Ribbit-Network/ribbit-network-solar/hardware/solar-charger.kicad_sch

## KiCad design hardware/solar-charger.kicad_sch (2022-02-11, an earlier design)

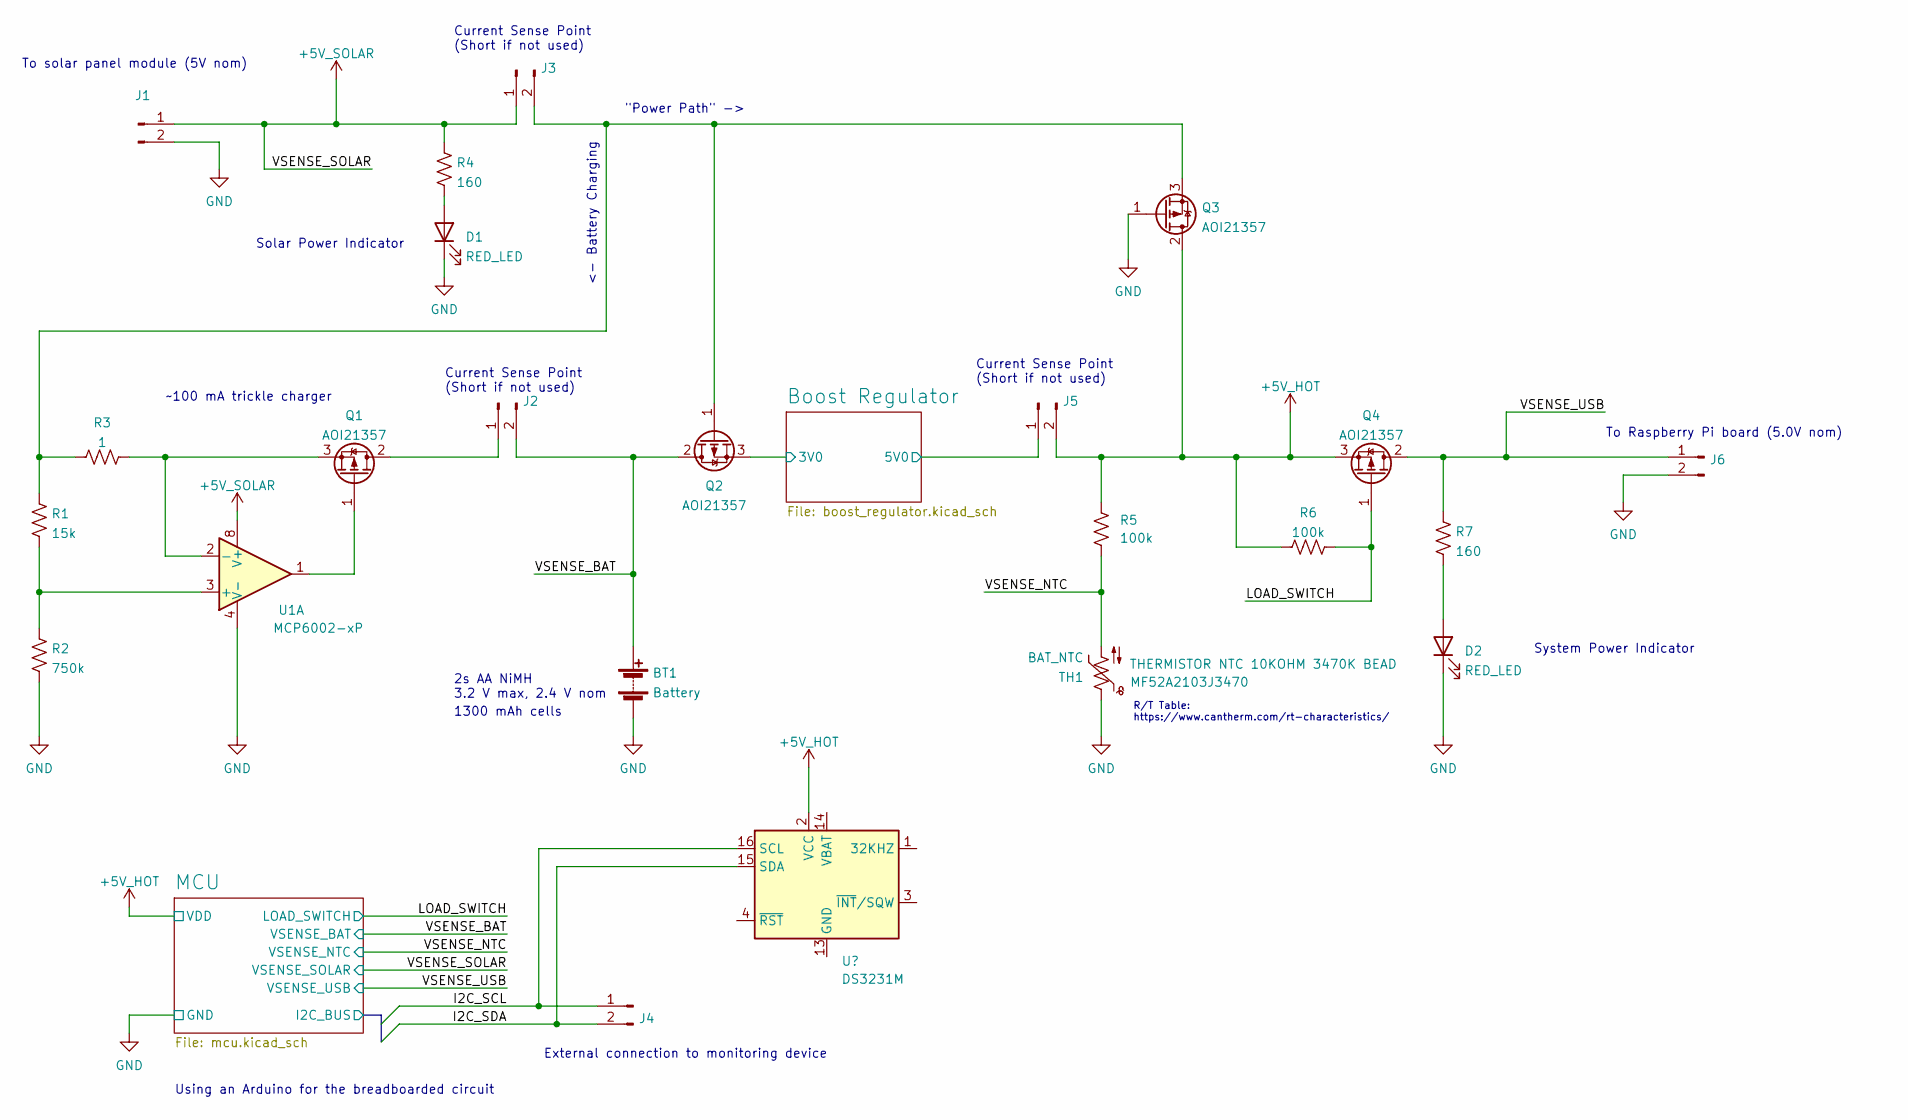
[picture p2: schematic solar-charger.kicad_sch]

Parts:
BT1: Battery
D1, D2: RED_LED
J1, J6: Conn_01x02_Male
J2, J3, J4: ISENSE_SOLAR
J5: ISENSE_DISCHARGE
Q1, Q2, Q3, Q4: AOI21357
R1: 15k
R2: 750k
R3: 1
R4, R7: 160
R5, R6: 100k
TH1: BAT_NTC; MPN MF52A2103J3470
U1: MCP6002-xP

Connections:
3V0: Q2.3 (S)
5V0: J5.1
+5V_HOT: J5.2, Q3.2 (D), Q4.3 (S), R5.1, R6.1
GND: BT1.2 (-), D1.1 (K), D2.1 (K), J1.2, J6.2, Q3.1 (G), R2.2, TH1.1, U1.4 (V-)
I2C_SCL: J4.1
I2C_SDA: J4.2
LOAD_SWITCH: Q4.1 (G), R6.2
unnamed: D1.2 (A), R4.2
unnamed: D2.2 (A), R7.2
unnamed: J2.1, Q1.2 (D)
unnamed: J3.2, Q2.1 (G), Q3.3 (S), R1.1, R3.1
unnamed: Q1.1 (G), U1.1
unnamed: Q1.3 (S), R3.2, U1.2 (-)
unnamed: R1.2, R2.1, U1.3 (+)
VSENSE_BAT: BT1.1 (+), J2.2, Q2.2 (D)
VSENSE_NTC: R5.2, TH1.2
VSENSE_SOLAR: J1.1, J3.1, R4.1
VSENSE_USB: J6.1, Q4.2 (D), R7.1

Notes on the sheet:
<- Battery Charging
To solar panel module (5V nom)
Solar Power Indicator
Current Sense Point (Short if not used)
~100 mA trickle charger
R/T Table: https://www.cantherm.com/rt-characteristics/
2s AA NiMH 3.2 V max, 2.4 V nom
"Power Path" ->
External connection to monitoring device
Using an Arduino for the breadboarded circuit
System Power Indicator
1300 mAh cells
To Raspberry Pi board (5.0V nom)
